adrianariton/OpenBook_UniProj_TSC/Images/display_home.png

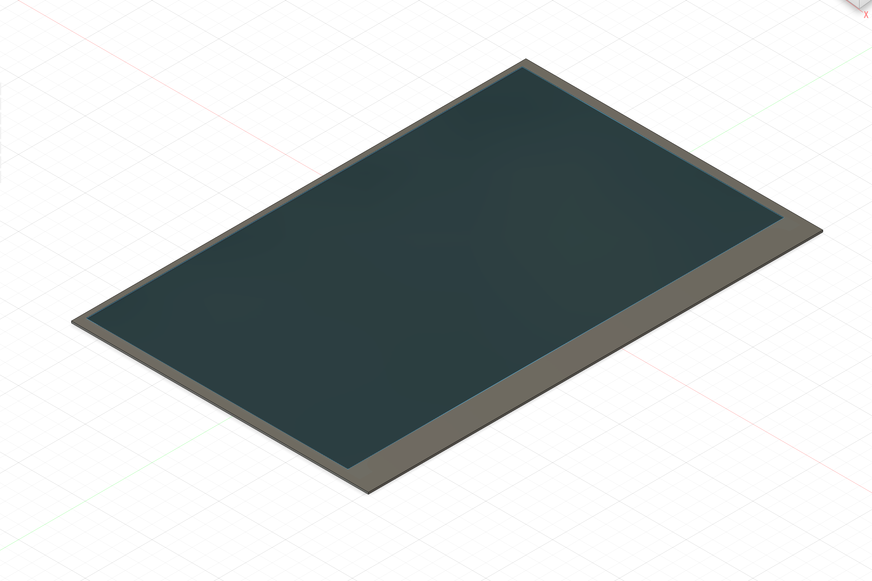
Images/display_home.png
