adrianariton/OpenBook_UniProj_TSC/Images/display_top.png

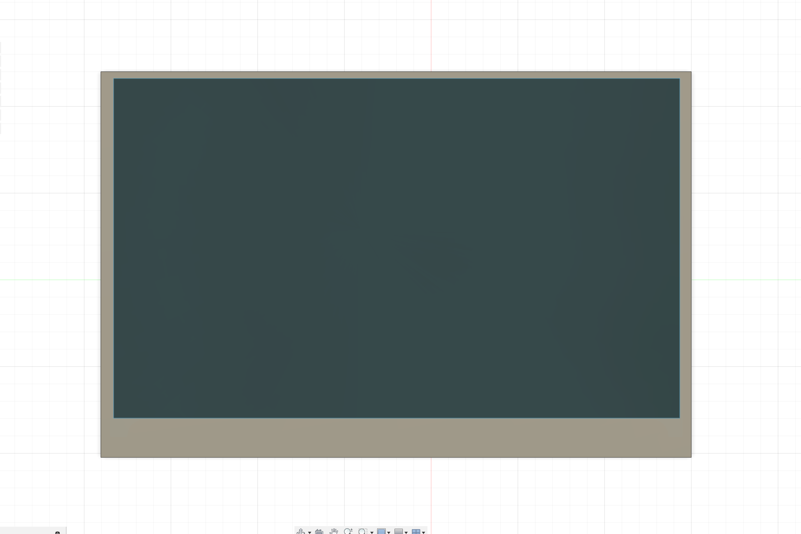
Images/display_top.png
